InfiniteTimeZ/ESP32-Media-Player/desktop-companion/network.py

import time
import asyncio
import re
import unicodedata
import logging

import discord_client
import hardware

_RECONCILE_INTERVAL = 1.0
_COMMAND_DEBOUNCE_SECONDS = 0.3
logger = logging.getLogger(__name__)


class VoiceRosterState:
    def __init__(self):
        self.users = {}
        self.last_roster_ids = []
        self.avatar_bound_at_index = {}
        self.avatar_index_epoch = {}
        self.cached_jpeg = {}
        self.cached_jpeg_hash = {}

class DiscordSyncState:
    def __init__(self):
        self.active_channel_id = None
        self.active_channel_name = ""
        self.last_command_time = {}
        self.active_rpc_client = None


roster = VoiceRosterState()
discord_state = DiscordSyncState()


def _sanitize_display_text(text, fallback=""):
    """Return text that the ESP32's built-in Montserrat fonts can render."""
    if not text:
        return fallback

    normalized = unicodedata.normalize("NFKD", str(text))
    ascii_text = normalized.encode("ascii", "ignore").decode("ascii")
    ascii_text = re.sub(r"\s+", " ", ascii_text)
    printable_text = "".join(
        char for char in ascii_text if 0x20 <= ord(char) <= 0x7E
    ).strip()

    return printable_text or fallback

_rpc_lock = asyncio.Lock()
avatar_send_lock = asyncio.Lock()

def _clear_avatar_bindings():
    roster.avatar_bound_at_index.clear()
    roster.avatar_index_epoch.clear()

def resync_hardware():
    hardware.send_voice_channel_name( discord_state.active_channel_name if discord_state.active_channel_id else "")
    if not discord_state.active_channel_id:
        hardware.send_voice_user_json({"count": 0, "width": 0, "height": 0, "users": []})
        _clear_avatar_bindings()
        return
    roster.last_roster_ids.clear()
    _clear_avatar_bindings()
    send_channel_users()


async def handle_discord_commands(rpc_client, cmd):
    if not rpc_client:
        return

    now = time.time()
    if now - discord_state.last_command_time.get(cmd, 0) < _COMMAND_DEBOUNCE_SECONDS:
        return
    discord_state.last_command_time[cmd] = now

    try:
        if cmd == "CMD:TOGGLE_MUTE":
            async with _rpc_lock:
                current_mute, current_deaf = await discord_client.get_voice_state(rpc_client) 
                new_mute = not current_mute
                await discord_client.set_mute(rpc_client, new_mute)
                
            hardware.send_discord_state(new_mute,current_deaf)
            logger.info("Discord mute changed to %s", new_mute)

        elif cmd == "CMD:TOGGLE_DEAFEN":
            async with _rpc_lock:
                current_mute, current_deaf = await discord_client.get_voice_state(rpc_client)
                new_deaf = not current_deaf
                await discord_client.set_deafen(rpc_client, new_deaf)

            hardware.send_discord_state(current_mute, new_deaf)
            logger.info("Discord deafen changed to %s", new_deaf)

        elif cmd == "CMD:LV_CALL":
            async with _rpc_lock:
                await discord_client.leave_discord_voice_channel(rpc_client)
            logger.info("Left Discord voice channel")

    except Exception:
        logger.exception("Discord command failed: %s", cmd)

async def init_discord_rpc():
    rpc = await discord_client.init_discord_rpc()

    if rpc is None:
        return None

    discord_state.active_rpc_client = rpc
    asyncio.create_task(_reconciler_loop(rpc))

    return rpc

def _layout_dimensions(user_count):
    if user_count <= 4:
        return 140, 150, 165
    elif user_count <= 8:
        return 110, 105, 120
    else:
        return 75, 85, 100

def send_channel_users():

    ordered_ids = list(roster.users.keys())[:15]
    user_count = len(ordered_ids)

    if user_count == 0:
        if roster.last_roster_ids:
            hardware.send_voice_user_json({"count": 0, "width": 0, "height": 0, "users": []})
            roster.last_roster_ids.clear()
            _clear_avatar_bindings()
        return 0

    target_size, card_w, card_h = _layout_dimensions(user_count)
    roster_changed = ordered_ids != roster.last_roster_ids

    if roster_changed:
        roster.last_roster_ids = ordered_ids.copy()

        user_json = {
            "count": user_count,
            "width": card_w,
            "height": card_h,
            "users": []
        }

        for uid in ordered_ids:
            user = roster.users[uid]
            display_name = _sanitize_display_text(user.get("name"), "Unknown")
            if len(display_name) > 12:
                display_name = display_name[:10] + ".."
            user_json["users"].append({
                "name": display_name
            })

        logger.info("Voice roster updated: %d users", user_count)
        hardware.send_voice_user_json(user_json)

    for idx, uid in enumerate(ordered_ids):
        user = roster.users[uid]
        ahash = user.get("avatar_hash")
        if not ahash:
            continue
        if roster.avatar_bound_at_index.get(idx) == (uid, ahash):
            continue
        roster.avatar_index_epoch[idx] = roster.avatar_index_epoch.get(idx, 0) + 1
        asyncio.create_task(_send_avatar(idx, uid, ahash, target_size, roster.avatar_index_epoch[idx]))

    return target_size

async def _send_avatar(idx, user_id, avatar_hash, target_size, epoch):
    jpeg_bytes = roster.cached_jpeg.get(user_id)
    if jpeg_bytes is None or roster.cached_jpeg_hash.get(user_id) != avatar_hash:
        await asyncio.sleep(0.5)
        url = f"https://cdn.discordapp.com/avatars/{user_id}/{avatar_hash}.png?size=128"
        jpeg_bytes = await asyncio.to_thread(discord_client.download_and_process_avatar, url, target_size)
        if not jpeg_bytes:
            return
        roster.cached_jpeg[user_id] = jpeg_bytes
        roster.cached_jpeg_hash[user_id] = avatar_hash

    async with avatar_send_lock:
        if roster.avatar_index_epoch.get(idx) != epoch:
            return
        hardware.send_avatar_image(idx, jpeg_bytes)
        roster.avatar_bound_at_index[idx] = (user_id, avatar_hash)
        logger.debug(
            "Sent Discord avatar for index %d (%d bytes)",
             idx,
            len(jpeg_bytes),
        )
        await asyncio.sleep(0.05)

def _user_from_state(state):
    user_info = state.get("user", {})
    return user_info.get("id"), {
        "name": state.get("nick") or user_info.get("global_name") or user_info.get("username", "Unknown"),
        "avatar_hash": user_info.get("avatar"),
    }

def _switch_channel(new_channel_id, data):
    discord_state.active_channel_id = new_channel_id
    roster.users.clear()
    _clear_avatar_bindings()

    if not new_channel_id:
        discord_state.active_channel_name = ""
        hardware.send_voice_channel_name("")
        send_channel_users()
        return

    roster.last_roster_ids.clear()

    for state in (data.get("voice_states", []) if data else [])[:15]:
        uid, user = _user_from_state(state)
        if uid:
            roster.users[uid] = user

    discord_state.active_channel_name = _sanitize_display_text(
        data.get("name") if data else None,
        "Voice Channel",
    )
    hardware.send_voice_channel_name(discord_state.active_channel_name)

    logger.info(
        "Discord voice channel changed to %s with %d members",
        new_channel_id,
        len(roster.users),
    )
    send_channel_users()

def _apply_roster(voice_states):
    new_users = {}
    for state in voice_states[:15]:
        uid, user = _user_from_state(state)
        if uid:
            new_users[uid] = user
    roster.users = new_users
    send_channel_users()

async def _reconcile(rpc_client):
    async with _rpc_lock:
        try:
            channel_fetch = await discord_client.get_selected_voice_channel(rpc_client)
        except Exception as exc:
            logger.debug("Discord channel fetch failed: %s", exc)
            channel_fetch = None
        try:
            voice_state = await discord_client.get_voice_state(rpc_client)
        except Exception as exc:
            logger.debug("Discord voice settings fetch failed: %s", exc)
            voice_state  = None

    data = channel_fetch.get("data") if channel_fetch else None
    new_channel_id = data.get("id") if data else None

    if new_channel_id != discord_state.active_channel_id:
        _switch_channel(new_channel_id, data)
    elif new_channel_id:
        _apply_roster(data.get("voice_states", []))

    if voice_state  is not None:
        mute, deaf = voice_state

        # Sent every tick to ESP32 stays sync'd
        # with Discord's state
        hardware.send_discord_state(mute, deaf)

async def _reconciler_loop(rpc_client):
    while discord_state.active_rpc_client is rpc_client:
        try:
            await _reconcile(rpc_client)
        except Exception:
           logger.exception("Unexpected error in Discord reconciliation loop")
        await asyncio.sleep(_RECONCILE_INTERVAL)
